cipher2infinity/Arduino-Electronics-circuit-PCB-Design-IOT-Programming/Hardware Descreption/2. Atmega256 Circuit/README.md

# Atmega256 Circuit Descreption
1.	Atmega256 microcontroller is the brain of the data logger.
2.	This circuit includes reset mechanism for microcontroller and external 16 MHz crystal facility
3.	The circuit includes 6 pin ICSP header to program bootloader in microcontroller.
4.	It also includes USB type B connector to program Microcontroller over UART0 Interface.
