cipher2infinity/Arduino-Electronics-circuit-PCB-Design-IOT-Programming/Datalogger Images/DataLogger Bootloader Programing Arrangement.jpg

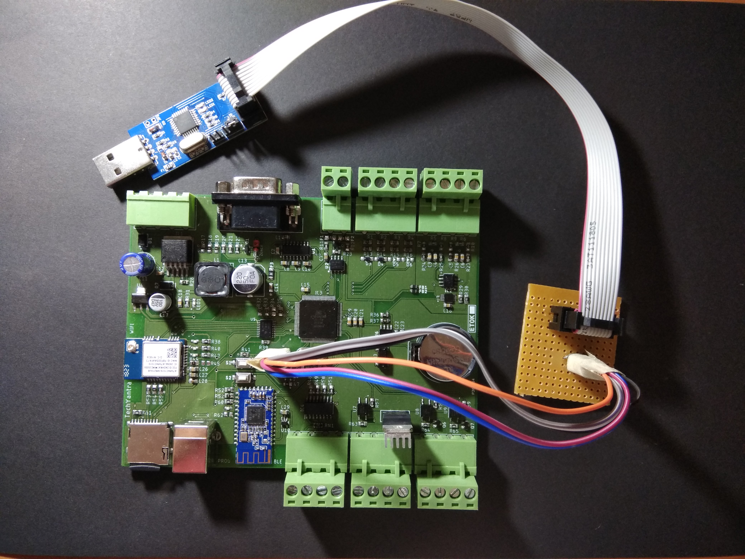
Datalogger Images/DataLogger Bootloader Programing Arrangement.jpg
