cipher2infinity/Arduino-Electronics-circuit-PCB-Design-IOT-Programming/Datalogger Images/DataLogger Programing Arrangement.jpg

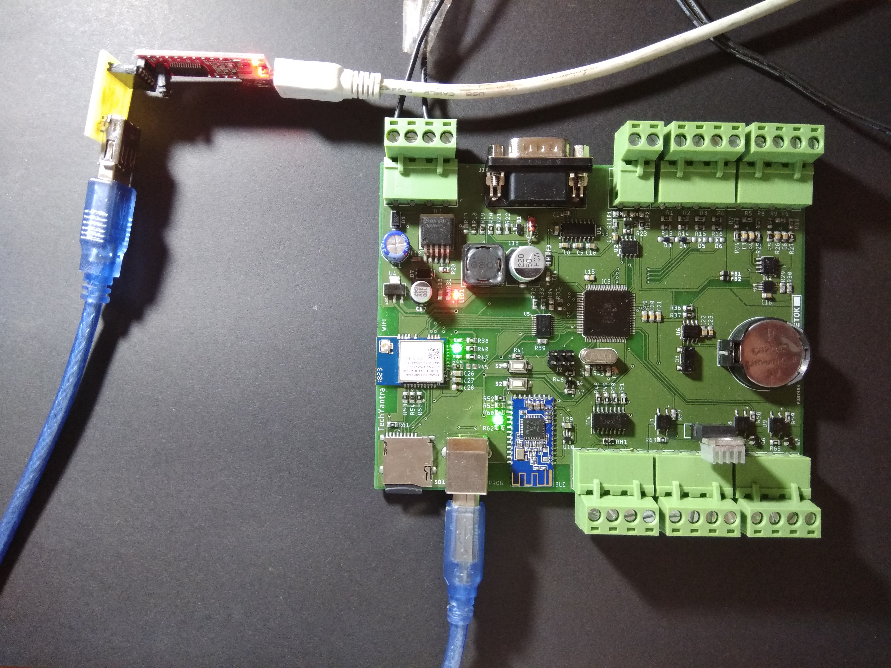
Datalogger Images/DataLogger Programing Arrangement.jpg
