cipher2infinity/Arduino-Electronics-circuit-PCB-Design-IOT-Programming/Datasheet/ascii-chars-landscape.jpg

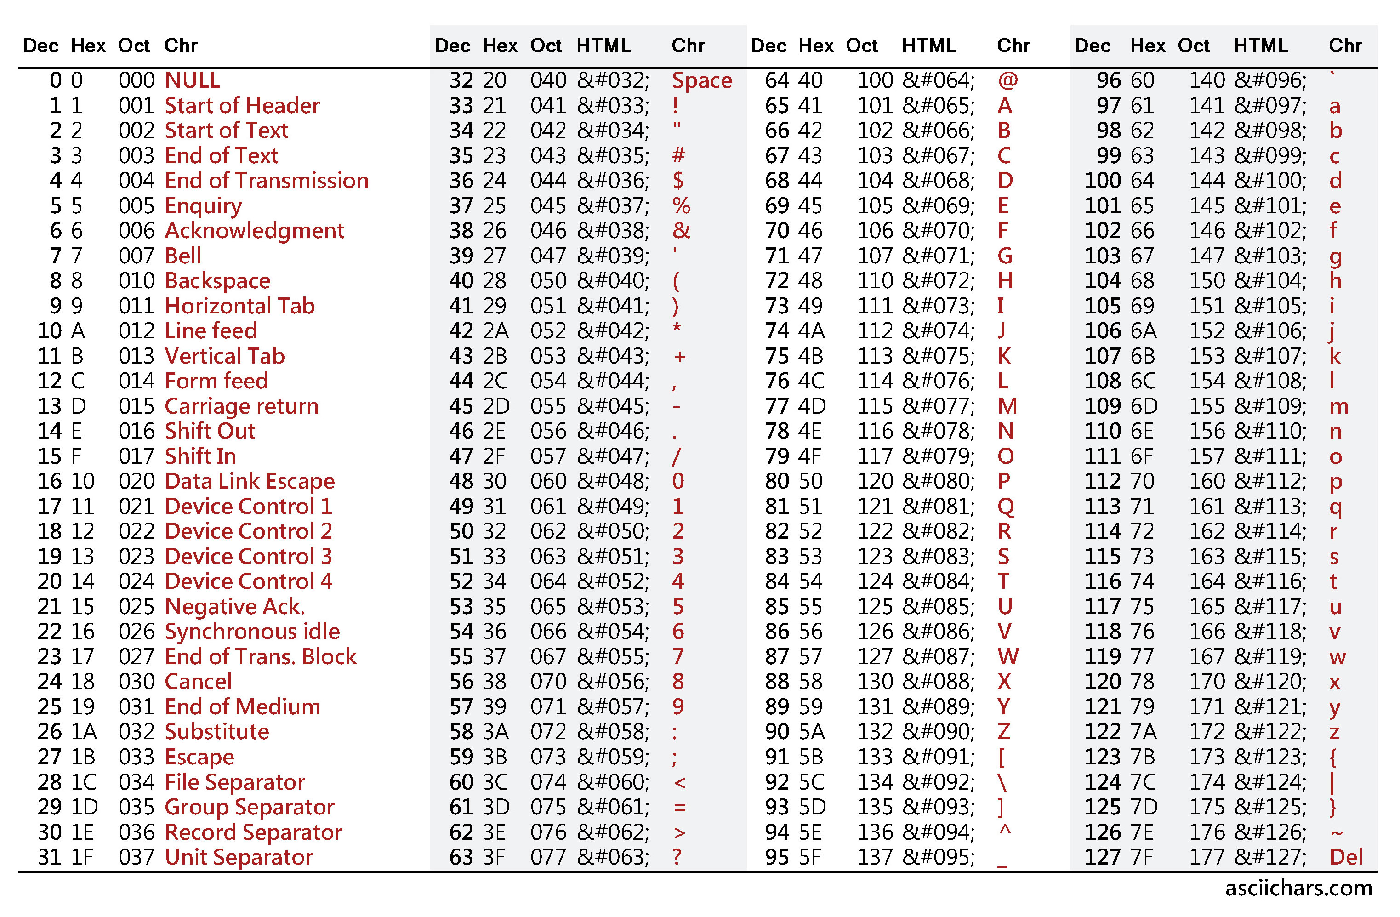
Datasheet/ascii-chars-landscape.jpg
