cipher2infinity/Arduino-Electronics-circuit-PCB-Design-IOT-Programming/Datasheet/SMD Capacitor size.png

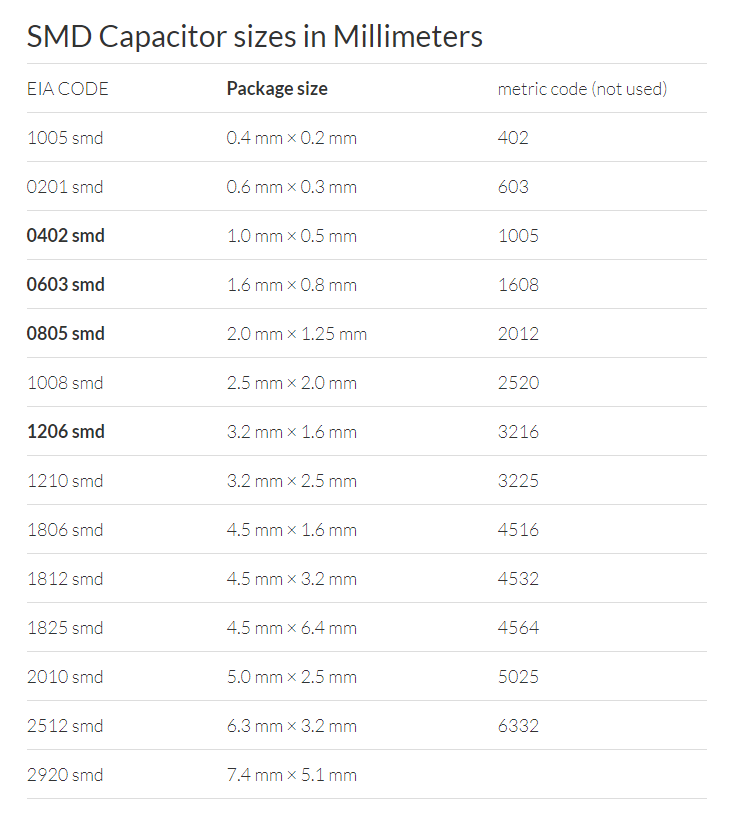
Datasheet/SMD Capacitor size.png
