cipher2infinity/Arduino-Electronics-circuit-PCB-Design-IOT-Programming/Datasheet/SMD Dimensions.jpg

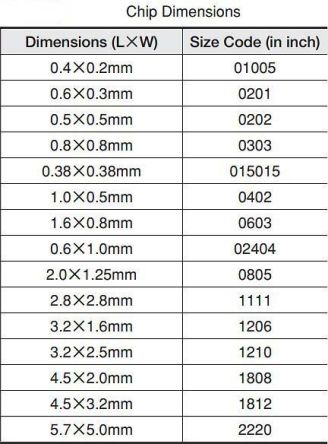
Datasheet/SMD Dimensions.jpg
