cipher2infinity/Arduino-Electronics-circuit-PCB-Design-IOT-Programming/Datasheet/Standerd Capacitor value.png

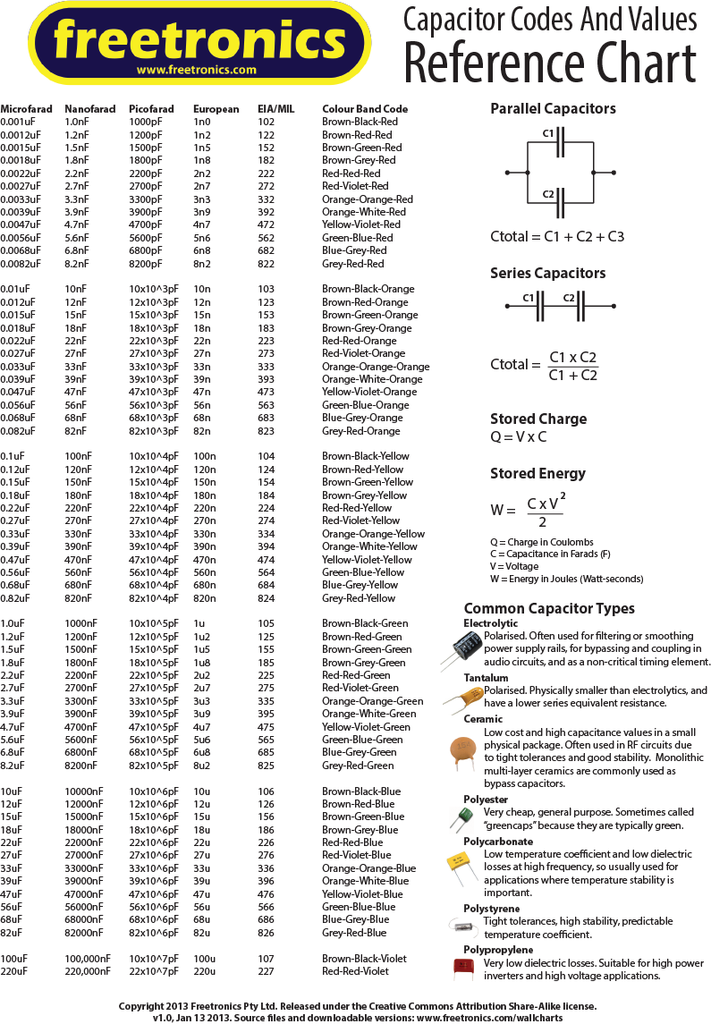
Datasheet/Standerd Capacitor value.png
