cipher2infinity/Arduino-Electronics-circuit-PCB-Design-IOT-Programming/Datasheet/Standerd Resistor value.jpg

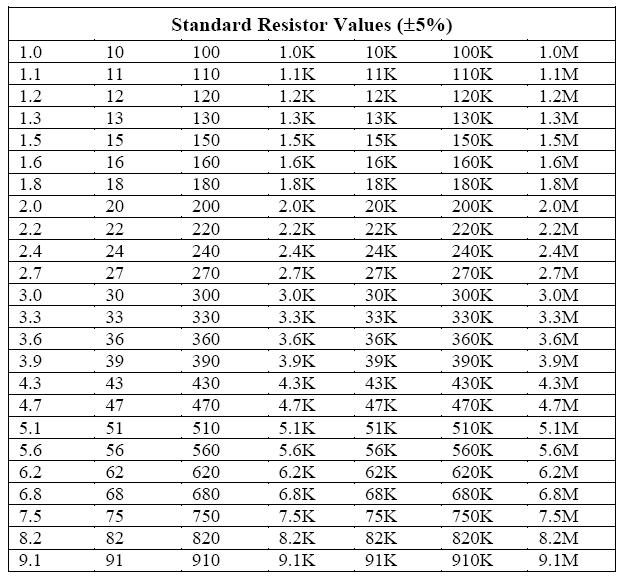
Datasheet/Standerd Resistor value.jpg
