cipher2infinity/Arduino-Electronics-circuit-PCB-Design-IOT-Programming/Datasheet/TVS Diodes List.png

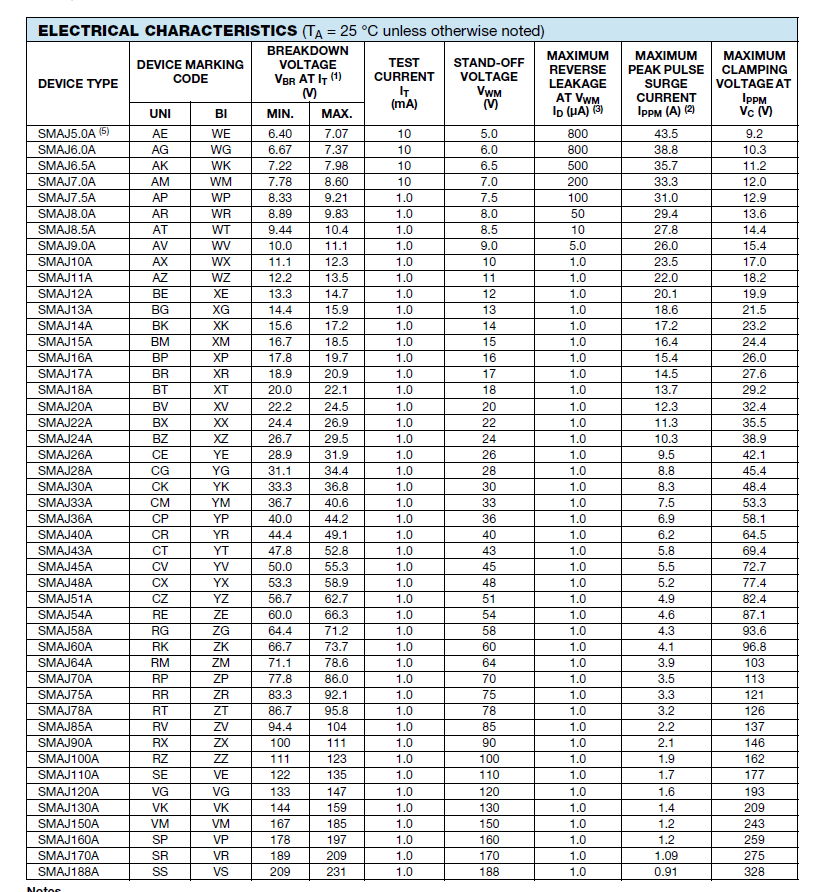
Datasheet/TVS Diodes List.png
