cipher2infinity/Arduino-Electronics-circuit-PCB-Design-IOT-Programming/Datasheet/Zener Diode List.png

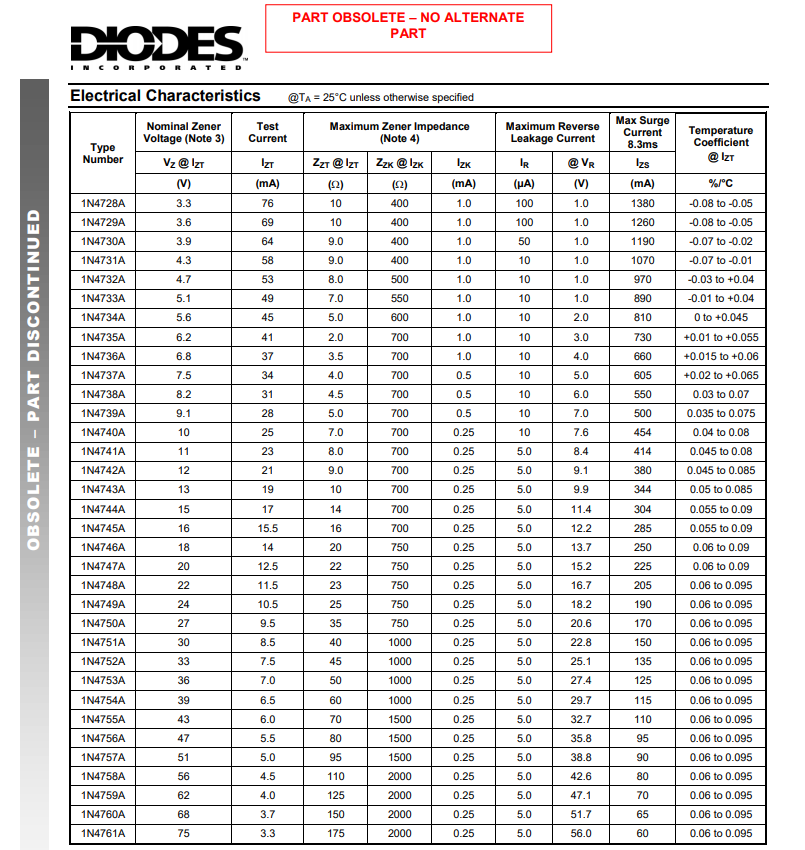
Datasheet/Zener Diode List.png
