cipher2infinity/Arduino-Electronics-circuit-PCB-Design-IOT-Programming/Design Files/Data Logger V3.1 Bottom.png

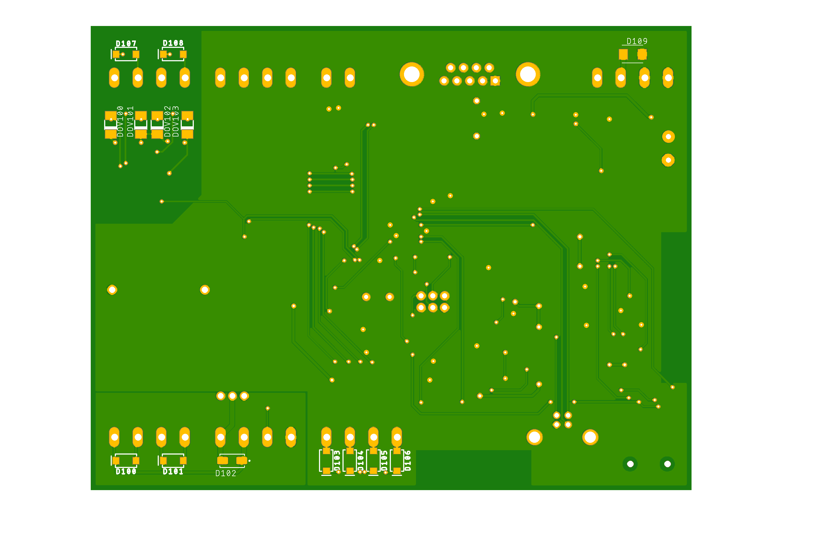
Design Files/Data Logger V3.1 Bottom.png
