cipher2infinity/Arduino-Electronics-circuit-PCB-Design-IOT-Programming/Hardware Descreption/1. Power Supply Circuit/Power Supply Design.png

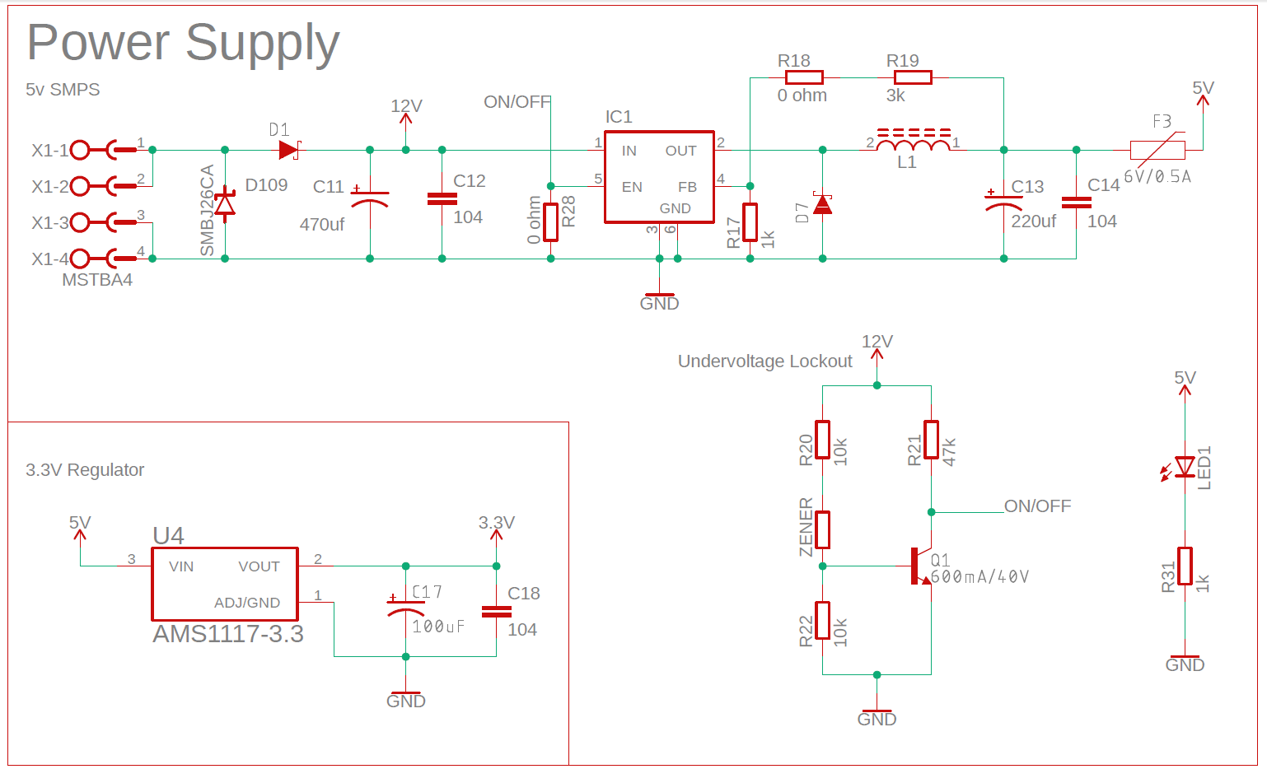
Hardware Descreption/1. Power Supply Circuit/Power Supply Design.png
