cipher2infinity/Arduino-Electronics-circuit-PCB-Design-IOT-Programming/Hardware Descreption/2. Atmega256 Circuit/Atmega256 Circuit.png

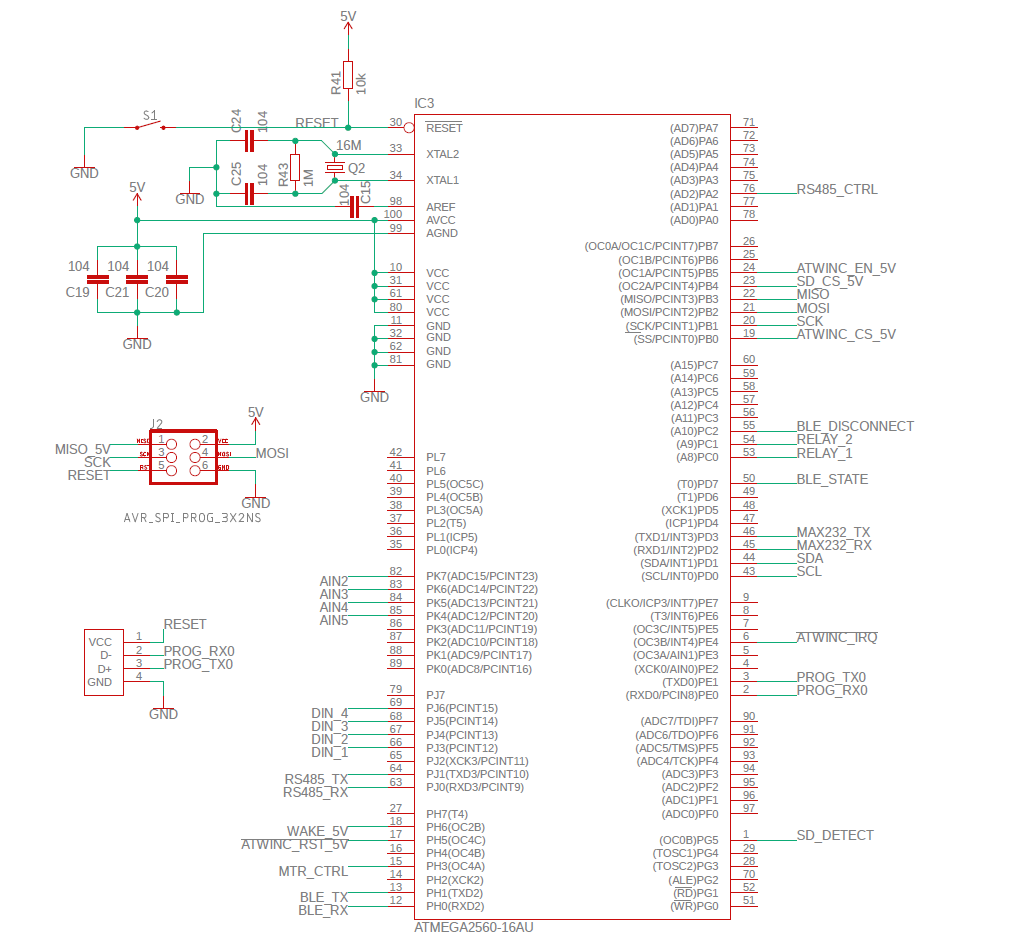
Hardware Descreption/2. Atmega256 Circuit/Atmega256 Circuit.png
