cipher2infinity/Arduino-Electronics-circuit-PCB-Design-IOT-Programming/Hardware Descreption/3. DC Motor Speed Controller Circuit/DC Motor Speed Controller circuit.png

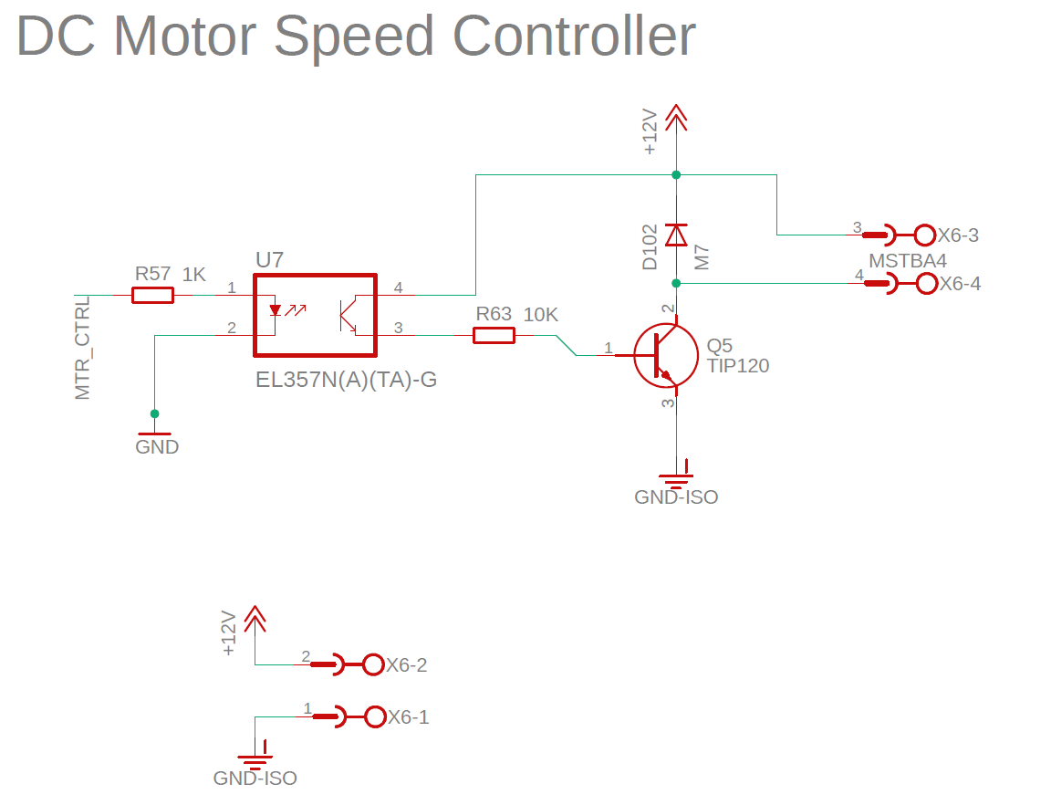
Hardware Descreption/3. DC Motor Speed Controller Circuit/DC Motor Speed Controller circuit.png
