cipher2infinity/Arduino-Electronics-circuit-PCB-Design-IOT-Programming/Hardware Descreption/5. RS485 Interface Circuit/RS485 Interface Circuit.png

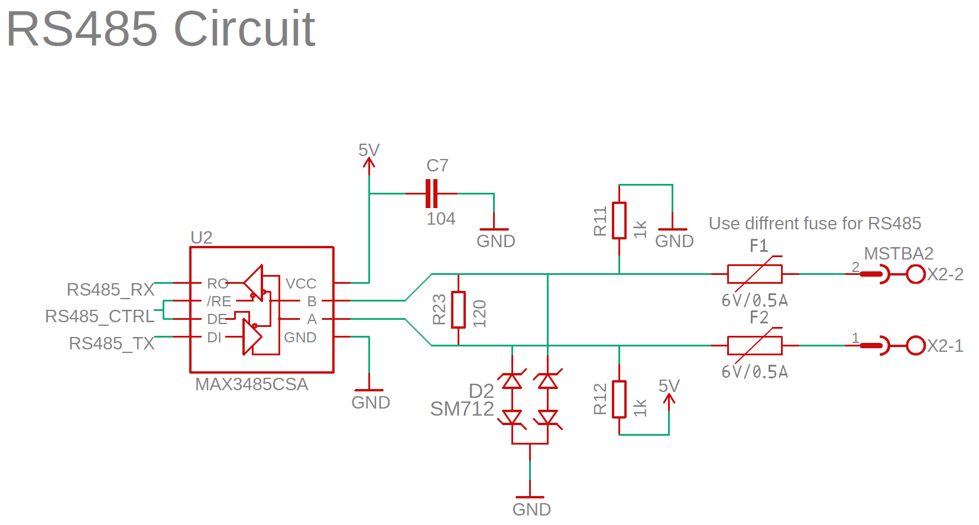
Hardware Descreption/5. RS485 Interface Circuit/RS485 Interface Circuit.png
