cipher2infinity/Arduino-Electronics-circuit-PCB-Design-IOT-Programming/Hardware Descreption/6. Relay Driver Circuit/Relay Driver Circuit.png

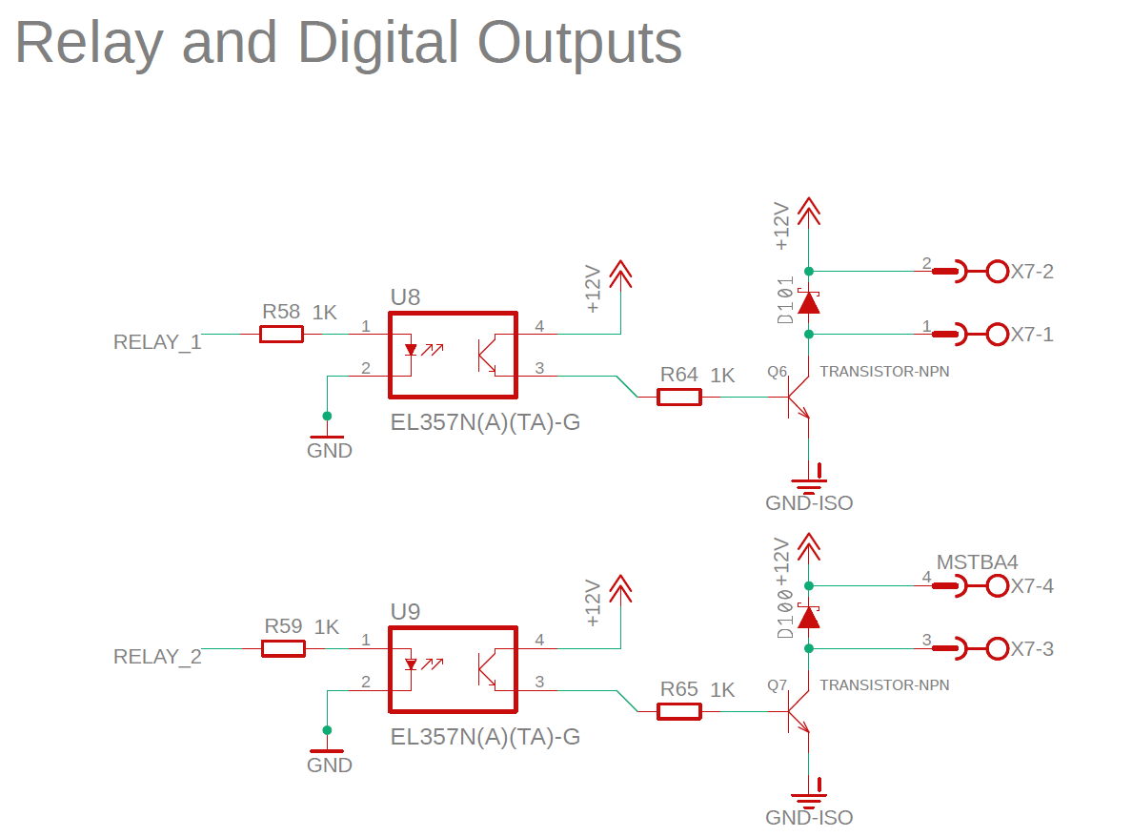
Hardware Descreption/6. Relay Driver Circuit/Relay Driver Circuit.png
