cipher2infinity/Arduino-Electronics-circuit-PCB-Design-IOT-Programming/Hardware Descreption/7. 0-10 V Analog Input Circuit/0-10 V Analog Input Circuit.png

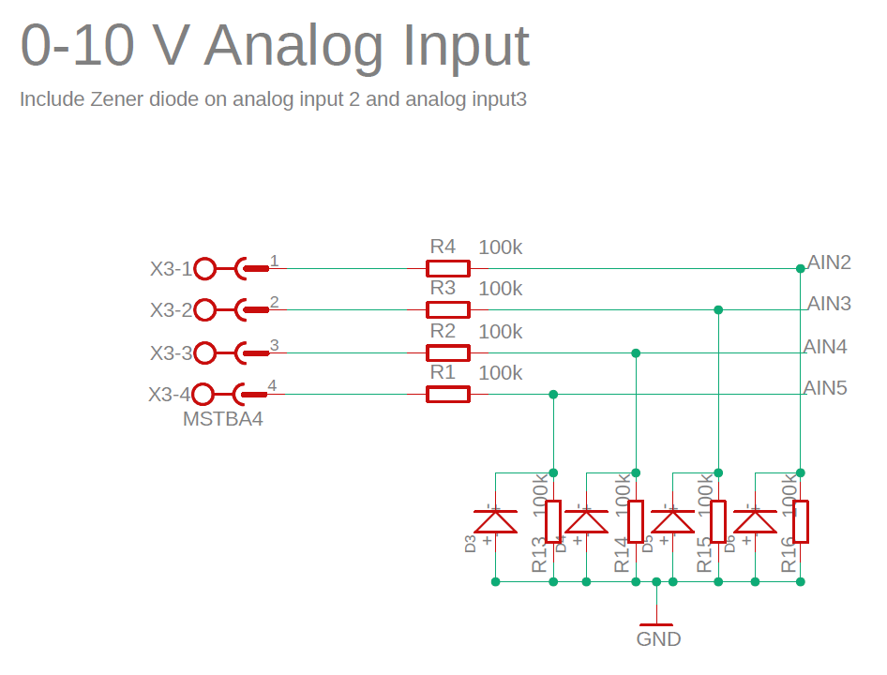
Hardware Descreption/7. 0-10 V Analog Input Circuit/0-10 V Analog Input Circuit.png
