cipher2infinity/Arduino-Electronics-circuit-PCB-Design-IOT-Programming/Hardware Descreption/8. RTC Circuit/RTC Circuit.png

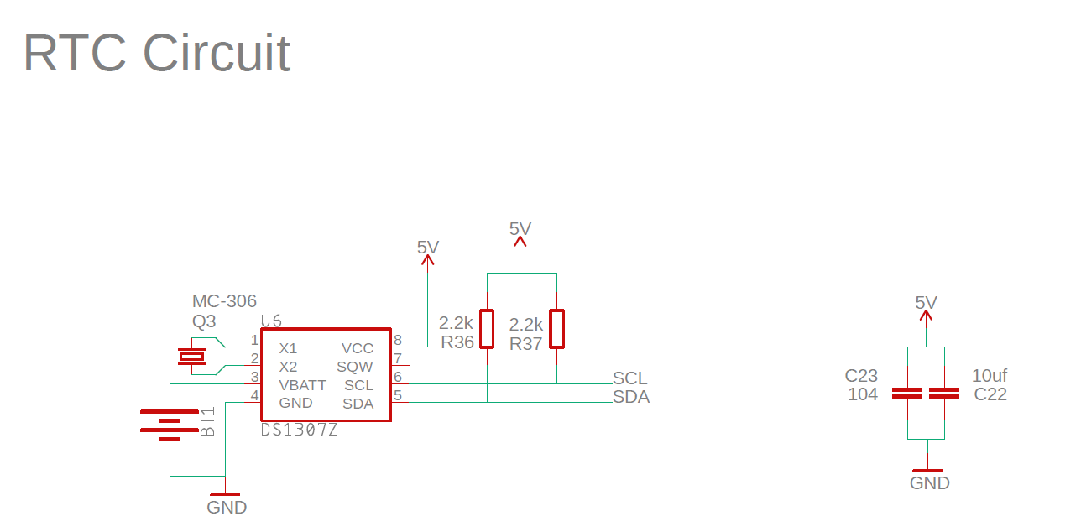
Hardware Descreption/8. RTC Circuit/RTC Circuit.png
