cipher2infinity/Arduino-Electronics-circuit-PCB-Design-IOT-Programming/Hardware Descreption/9. 4-20 mA Circuit/4-20 mA circuit.png

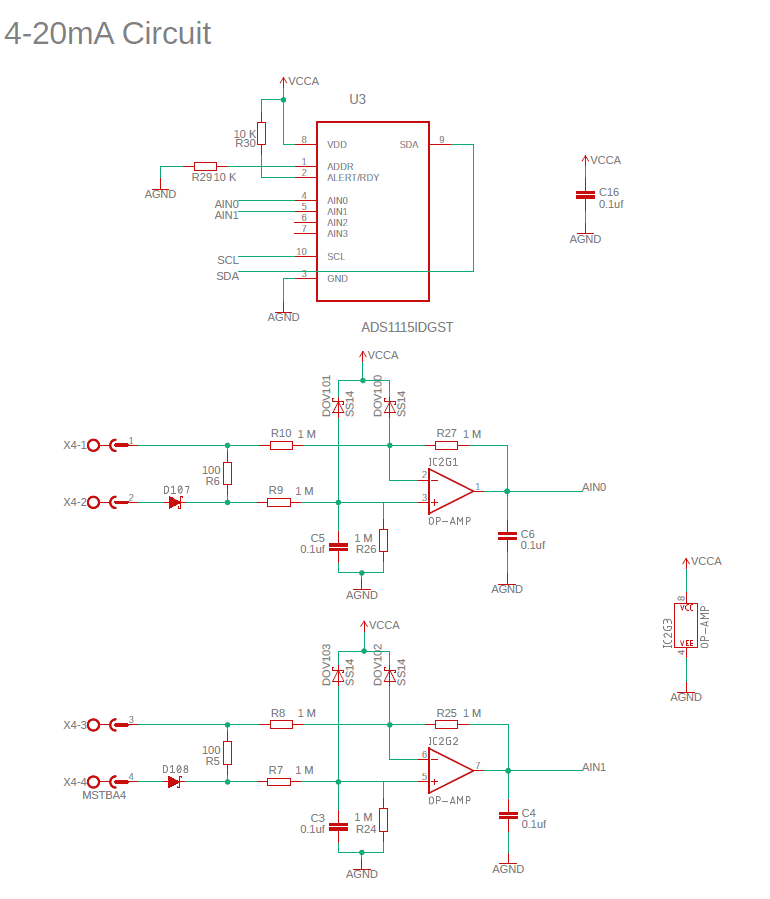
Hardware Descreption/9. 4-20 mA Circuit/4-20 mA circuit.png
