cipher2infinity/Arduino-Electronics-circuit-PCB-Design-IOT-Programming/Hardware Descreption/11. WiFi Module Circuit/WiFi Module Circuit.png

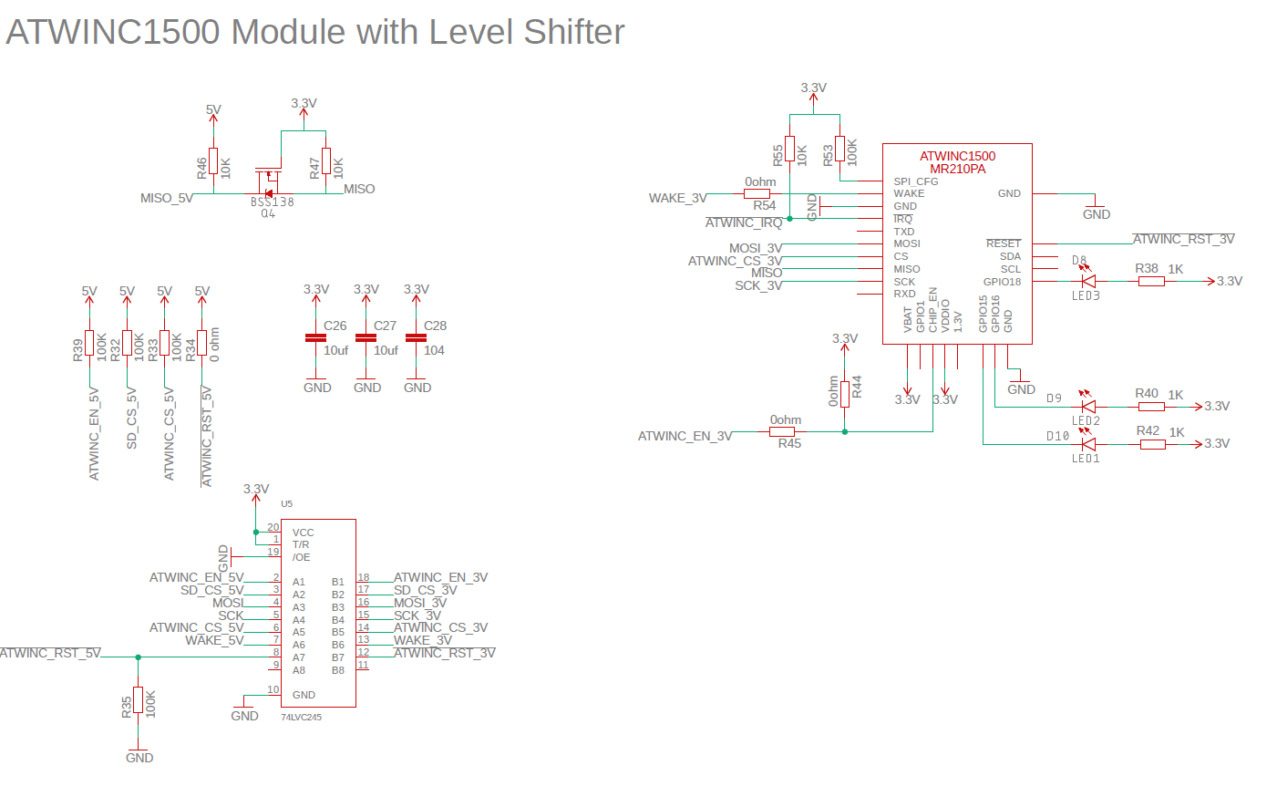
Hardware Descreption/11. WiFi Module Circuit/WiFi Module Circuit.png
