cipher2infinity/Arduino-Electronics-circuit-PCB-Design-IOT-Programming/Hardware Descreption/13. RS232 Interface Circuit/RS232 Interface Circuit.png

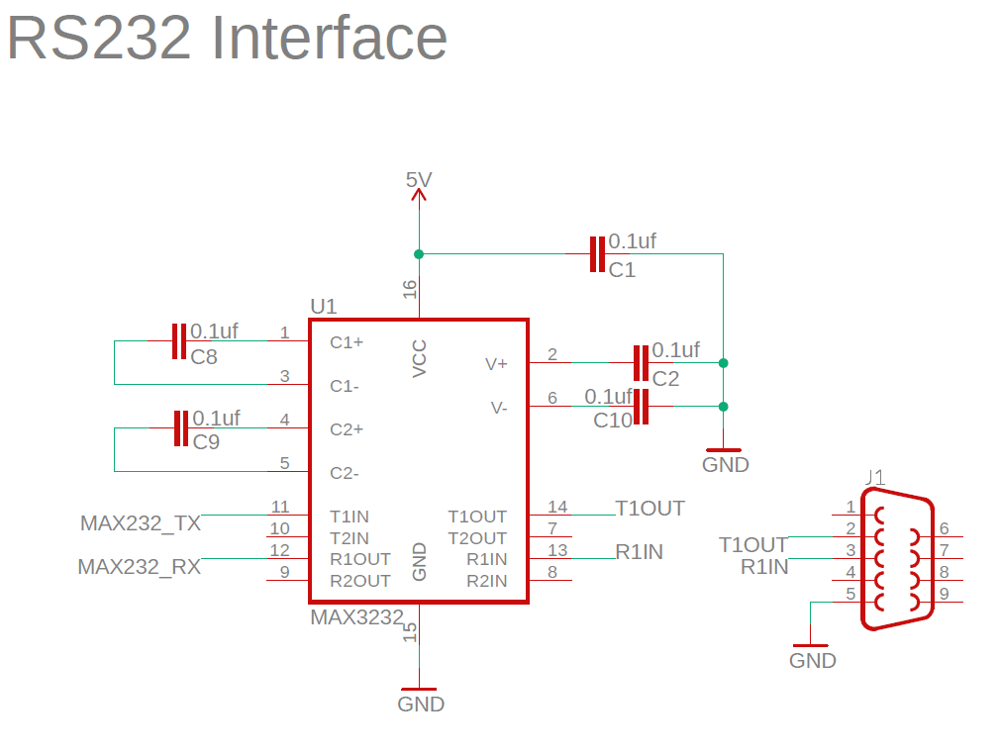
Hardware Descreption/13. RS232 Interface Circuit/RS232 Interface Circuit.png
